Grazen0/yuyu80/kicad/yuyu80.kicad_sch

## KiCad design kicad/yuyu80.kicad_sch (2026-08-03)

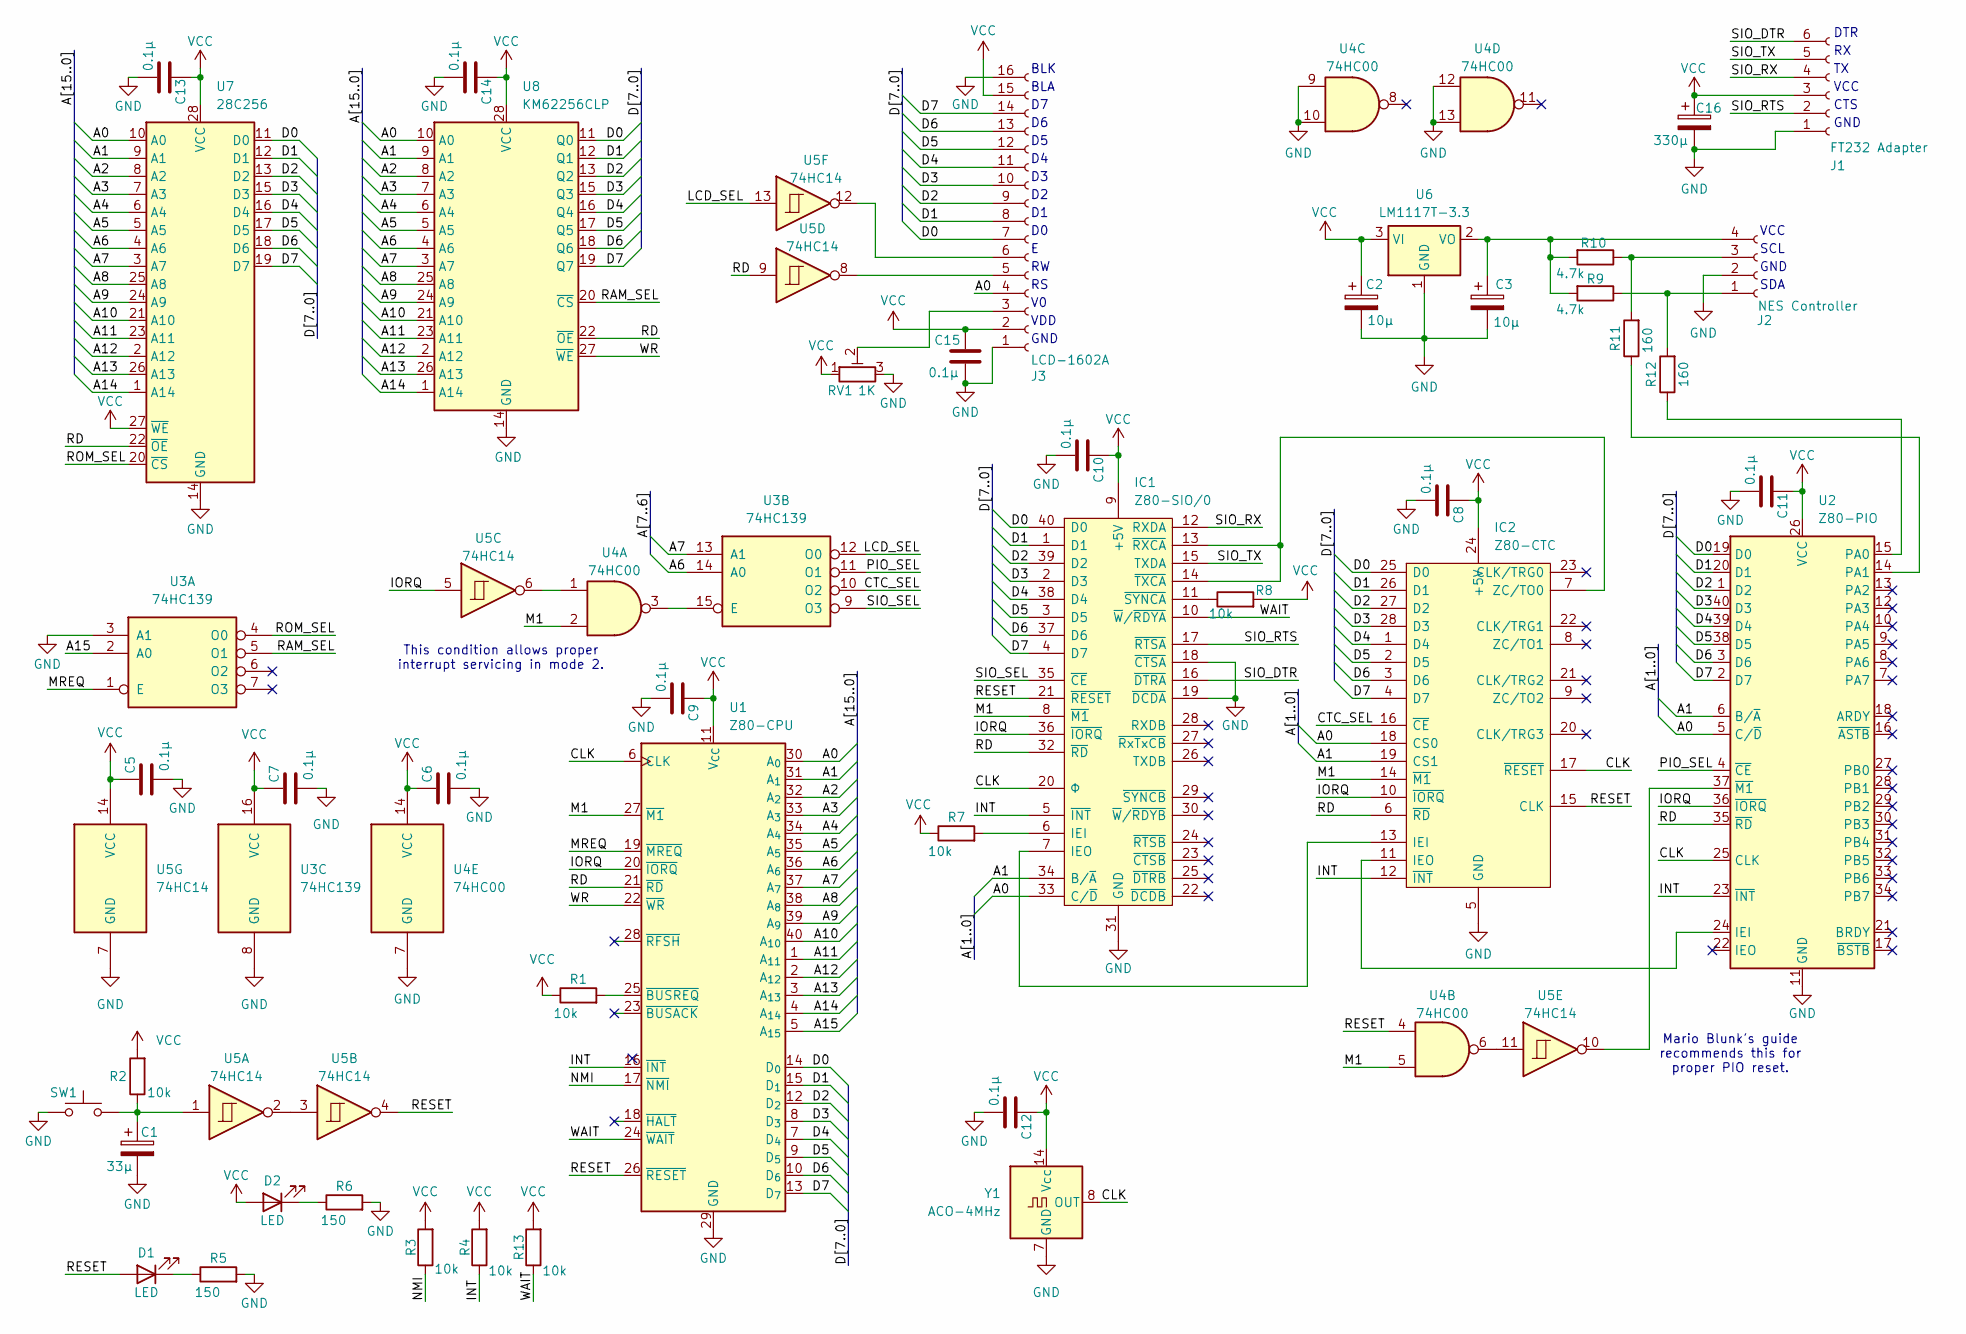
[picture p4: schematic yuyu80.kicad_sch]

Parts:
C1: 33µ; CP_Radial_D4.0mm_P1.50mm
C2, C3: 10µ; CP_Radial_D5.0mm_P2.50mm
C5, C6, C7, C8, C9, C10, C11, C12, C13, C14, C15: 0.1µ; C_Disc_D5.0mm_W2.5mm_P2.50mm
C16: 330µ; CP_Radial_D8.0mm_P3.80mm
D1, D2: LED; LED_D4.0mm
IC1: Z80-SIO/0; DIP-40_W15.24mm_Socket; Manufacturer_Part_Number Z84C4206PEG; Mouser Part Number 692-Z84C4206PEG
IC2: Z80-CTC; DIP-28_W15.24mm_Socket; Manufacturer_Part_Number Z84C3010PEG; Mouser Part Number 692-Z84C3010PEG
J1: FT232 Adapter; PinSocket_1x06_P2.54mm_Horizontal
J2: NES Controller; PinSocket_1x04_P2.54mm_Horizontal
J3: LCD-1602A; PinSocket_1x16_P2.54mm_Vertical
R1, R2, R3, R4, R7, R8, R13: 10k; R_Axial_DIN0207_L6.3mm_D2.5mm_P10.16mm_Horizontal
R5, R6: 150; R_Axial_DIN0207_L6.3mm_D2.5mm_P10.16mm_Horizontal
R9, R10: 4.7k; R_Axial_DIN0207_L6.3mm_D2.5mm_P10.16mm_Horizontal
R11, R12: 160; R_Axial_DIN0207_L6.3mm_D2.5mm_P10.16mm_Horizontal
RV1: 1K; Potentiometer_Vishay_T93YA_Vertical
SW1: SW_PUSH_6mm
U1: Z80-CPU; DIP-40_W15.24mm_Socket
U2: Z80-PIO; DIP-40_W15.24mm_Socket
U3: 74HC139; DIP-16_W7.62mm_Socket
U4: 74HC00; DIP-14_W7.62mm_Socket
U5: 74HC14
U6: LM1117T-3.3; TO-220-3_Horizontal_TabDown
U7: 28C256; DIP_Socket-28_W11.9mm_W12.7mm_W15.24mm_W17.78mm_W18.5mm_3M_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
U8: KM62256CLP; DIP-28_W15.24mm_Socket
Y1: ACO-4MHz; Oscillator_DIP-14

Connections:
A0: IC1.33 (C/~D), IC2.18 (CS0), J3.4, U1.30 (A_{0}), U2.5 (C/~D), U7.10 (A0), U8.10 (A0)
A1: IC1.34 (B/~A), IC2.19 (CS1), U1.31 (A_{1}), U2.6 (B/~A), U7.9 (A1), U8.9 (A1)
A2: U1.32 (A_{2}), U7.8 (A2), U8.8 (A2)
A3: U1.33 (A_{3}), U7.7 (A3), U8.7 (A3)
A4: U1.34 (A_{4}), U7.6 (A4), U8.6 (A4)
A5: U1.35 (A_{5}), U7.5 (A5), U8.5 (A5)
A6: U1.36 (A_{6}), U3.14 (A0), U7.4 (A6), U8.4 (A6)
A7: U1.37 (A_{7}), U3.13 (A1), U7.3 (A7), U8.3 (A7)
A8: U1.38 (A_{8}), U7.25 (A8), U8.25 (A8)
A9: U1.39 (A_{9}), U7.24 (A9), U8.24 (A9)
A10: U1.40 (A_{10}), U7.21 (A10), U8.21 (A10)
A11: U1.1 (A_{11}), U7.23 (A11), U8.23 (A11)
A12: U1.2 (A_{12}), U7.2 (A12), U8.2 (A12)
A13: U1.3 (A_{13}), U7.26 (A13), U8.26 (A13)
A14: U1.4 (A_{14}), U7.1 (A14), U8.1 (A14)
A15: U1.5 (A_{15}), U3.2 (A0)
CLK: IC1.20 (Φ), IC2.17 (~RESET), U1.6 (CLK), U2.25 (CLK), Y1.8 (OUT)
CTC_SEL: IC2.16 (~CE), U3.10 (O2)
D0: IC1.40 (D0), IC2.25 (D0), J3.7, U1.14 (D_{0}), U2.19 (D0), U7.11 (D0), U8.11 (Q0)
D1: IC1.1 (D1), IC2.26 (D1), J3.8, U1.15 (D_{1}), U2.20 (D1), U7.12 (D1), U8.12 (Q1)
D2: IC1.39 (D2), IC2.27 (D2), J3.9, U1.12 (D_{2}), U2.1 (D2), U7.13 (D2), U8.13 (Q2)
D3: IC1.2 (D3), IC2.28 (D3), J3.10, U1.8 (D_{3}), U2.40 (D3), U7.15 (D3), U8.15 (Q3)
D4: IC1.38 (D4), IC2.1 (D4), J3.11, U1.7 (D_{4}), U2.39 (D4), U7.16 (D4), U8.16 (Q4)
D5: IC1.3 (D5), IC2.2 (D5), J3.12, U1.9 (D_{5}), U2.38 (D5), U7.17 (D5), U8.17 (Q5)
D6: IC1.37 (D6), IC2.3 (D6), J3.13, U1.10 (D_{6}), U2.3 (D6), U7.18 (D6), U8.18 (Q6)
D7: IC1.4 (D7), IC2.4 (D7), J3.14, U1.13 (D_{7}), U2.2 (D7), U7.19 (D7), U8.19 (Q7)
GND: C1.2, C2.2, C3.2, C5.2, C6.2, C7.2, C8.2, C9.2, C10.2, C11.2, C12.2, C13.2, C14.2, C15.2, C16.2, IC1.18 (~CTSA), IC1.19 (~DCDA), IC1.31 (GND), IC2.5 (GND), J1.1, J2.2, J3.1, J3.16, R5.2, R6.2, RV1.3, SW1.1, U1.29 (GND), U2.11 (GND), U3.3 (A1), U3.8 (GND), U4.7 (GND), U4.9, U4.10, U4.12, U4.13, U5.7 (GND), U6.1 (GND), U7.14 (GND), U8.14 (GND), Y1.7 (GND)
INT: IC1.5 (~INT), IC2.12 (~INT), R4.1, U1.16 (~INT), U2.23 (~INT)
IORQ: IC1.36 (~IORQ), IC2.10 (~IORQ), U1.20 (~IORQ), U2.36 (~IORQ), U5.5
LCD_SEL: U3.12 (O0), U5.13
M1: IC1.8 (~M1), IC2.14 (~M1), U1.27 (~M1), U4.2, U4.5
MREQ: U1.19 (~MREQ), U3.1 (E)
NMI: R3.1, U1.17 (~NMI)
unnamed: C1.1, R2.1, SW1.2, U5.1
unnamed: C3.1, J2.4, R9.2, R10.2, U6.2 (VO)
unnamed: D1.1 (K), R5.1
unnamed: D2.1 (K), R6.1
unnamed: IC1.6 (IEI), R7.2
unnamed: IC1.7 (IEO), IC2.13 (IEI)
unnamed: IC1.11 (~SYNCA), R8.1
unnamed: IC1.13 (~RXCA), IC1.14 (~TXCA), IC2.7 (ZC/TO0)
unnamed: IC2.11 (IEO), U2.24 (IEI)
unnamed: J2.1, R9.1, R12.2
unnamed: J2.3, R10.1, R11.2
unnamed: J3.3, RV1.2
unnamed: J3.5, U5.8
unnamed: J3.6, U5.12
unnamed: R1.2, U1.25 (~BUSREQ)
unnamed: R11.1, U2.14 (PA1)
unnamed: R12.1, U2.15 (PA0)
unnamed: U2.37 (~M1), U5.10
unnamed: U3.15 (E), U4.3
unnamed: U4.1, U5.6
unnamed: U4.6, U5.11
unnamed: U5.2, U5.3
PIO_SEL: U2.4 (~CE), U3.11 (O1)
RAM_SEL: U3.5 (O1), U8.20 (~CS)
RD: IC1.32 (~RD), IC2.6 (~RD), U1.21 (~RD), U2.35 (~RD), U5.9, U7.22 (~OE), U8.22 (~OE)
RESET: D1.2 (A), IC1.21 (~RESET), IC2.15 (CLK), U1.26 (~RESET), U4.4, U5.4
ROM_SEL: U3.4 (O0), U7.20 (~CS)
SIO_DTR: IC1.16 (~DTRA), J1.6
SIO_RTS: IC1.17 (~RTSA), J1.2
SIO_RX: IC1.12 (RXDA), J1.4
SIO_SEL: IC1.35 (~CE), U3.9 (O3)
SIO_TX: IC1.15 (TXDA), J1.5
VCC: C2.1, C5.1, C6.1, C7.1, C8.1, C9.1, C10.1, C11.1, C12.1, C13.1, C14.1, C15.1, C16.1, D2.2 (A), IC1.9 (+5V), IC2.24 (+5V), J1.3, J3.2, J3.15, R1.1, R2.2, R3.2, R4.2, R7.1, R8.2, R13.2, RV1.1, U1.11 (V_{CC}), U2.26 (VCC), U3.16 (VCC), U4.14 (VCC), U5.14 (VCC), U6.3 (VI), U7.27 (~WE), U7.28 (VCC), U8.28 (VCC), Y1.14 (Vcc)
WAIT: IC1.10 (~W/~RDYA), R13.1, U1.24 (~WAIT)
WR: U1.22 (~WR), U8.27 (~WE)

Notes on the sheet:
GND
SDA
VCC
CTS
Mario Blunk's guide recommends this for proper PIO reset.
This condition allows proper interrupt servicing in mode 2.
BLK
VDD
DTR
SCL
BLA
