Grazen0/yuyu80/zetris/src/lcd.asm

    .include "lcd.inc"
    .include "system.inc"

    .module lcd

INSTR_SET_DDRAM equ $80

INSTR_DISPLAY_CTRL equ %00001000

; ------------------------------------------------------------------------------
; Waits for the LCD's busy flag to go low.
;
; In:   -
; Out:  -
; Destroys: a
; ------------------------------------------------------------------------------
busy_wait:
    in      a, (LCD_CTRL) 
    and     $80
    ret     z
    jr      busy_wait

; ------------------------------------------------------------------------------
; Sends an instruction to the LCD.
;
; In:       a = instruction to send
; Out:      -
; Destroys: -
; ------------------------------------------------------------------------------
send_instr:
    push    af
    call    busy_wait
    pop     af
    out     (LCD_CTRL), a
    ret


; ------------------------------------------------------------------------------
; Positions the LCD's cursor at the beginning of the first line.
;
; In:       -
; Out:      -
; Destroys: a
; ------------------------------------------------------------------------------
move_cursor_line_1:
    ld      a, INSTR_SET_DDRAM | $00
    jp      send_instr

; ------------------------------------------------------------------------------
; Positions the LCD's cursor at the beginning of the second line.
;
; In:       -
; Out:      -
; Destroys: a
; ------------------------------------------------------------------------------
move_cursor_line_2:
    ld      a, INSTR_SET_DDRAM | $40
    jp      send_instr

; ------------------------------------------------------------------------------
; Initializes the LCD. Must be called before any other LCD subroutines.
;
; In:       -
; Out:      -
; Destroys: a
; ------------------------------------------------------------------------------
init:
    ld      a, %00111000    ; interface data length & misc
    ;              |||
    ;              ||+--- 5x11/5x8 font = 0 (5x8)
    ;              |+---- 2/1 lines = 1 (1 line)
    ;              +----- 8/4-bit mode = 1 (8-bit)
    call    send_instr

    ld      a, %00000010    ; return home
    call    send_instr

    ld      a, %00000110    ; entry mode set
    ;                 ||
    ;                 |+- shift display = 0
    ;                 +-- inc/dec cursor = 1 (inc)
    call    send_instr


    ld      a, %00001111    ; display on/off control
    ;                |||
    ;                ||+- cursor blinking = 1
    ;                |+-- cursor enable = 1
    ;                +--- display enable = 1
    call    send_instr

    ld      a, %00000001    ; clear display
    call    send_instr

    jp      move_cursor_line_1

; ------------------------------------------------------------------------------
; Prints a character to the LCD.
;
; In:       c = character to print
; Out:      -
; Destroys: a
; ------------------------------------------------------------------------------
print_char:
    call    busy_wait
    ld      a, c
    out     (LCD_DATA), a
    ret

; ------------------------------------------------------------------------------
; Fills the remainder of the LCD's current line with " ".
;
; In:       -
; Out:      -
; Destroys: bc
; ------------------------------------------------------------------------------
clear_to_eol:
    ld      b, 16
    ld      c, ' '

.loop
    call    print_char
    djnz    .loop

    ret


; ------------------------------------------------------------------------------
; Prints a null-terminated string to the LCD.
;
; In:       hl = pointer to the string to print
; Out:      -
; Destroys: a, c, hl
; ------------------------------------------------------------------------------
print:
    ld      a, (hl)
    or      a
    ret     z

    ld      c, a
    call    print_char
    inc     hl
    jr      print

; ------------------------------------------------------------------------------
; Prints a byte in hex format to the LCD.
;
; In:       d = byte to print
; Out:      -
; Destroys: a, c
; ------------------------------------------------------------------------------
print_hex:
    ld      a, d
    .4      srl     a
    call    @conv.digit_to_hex
    ld      c, a
    call    print_char

    ld      a, d
    and     $0F
    call    @conv.digit_to_hex
    ld      c, a
    jp      print_char

; ------------------------------------------------------------------------------
; Prints a byte in binary format to the LCD.
;
; In:       d = byte to print
; Out:      -
; Destroys: a, bc
; ------------------------------------------------------------------------------
print_bin:
    ld      b, 8
.loop:
    rlc     d
    ld      a, '0'
    adc     0
    ld      c, a
    call    print_char

    djnz    .loop
    ret


; ------------------------------------------------------------------------------
; Prints a 16-bit unsigned number to the LCD.
;
; In:       hl = number to print
; Out:      -
; Destroys: a, bc, de, hl
; ------------------------------------------------------------------------------
print_num:
    ld      bc, lcd_num_str_buf
    call    @conv.num_to_str
    jp      print

    .endmodule
